SoloScriptSage/xNAV650-Ouster-Adapter-Enclosure/xnav650.kicad_sch

## KiCad design xnav650.kicad_sch (2025-11-14)

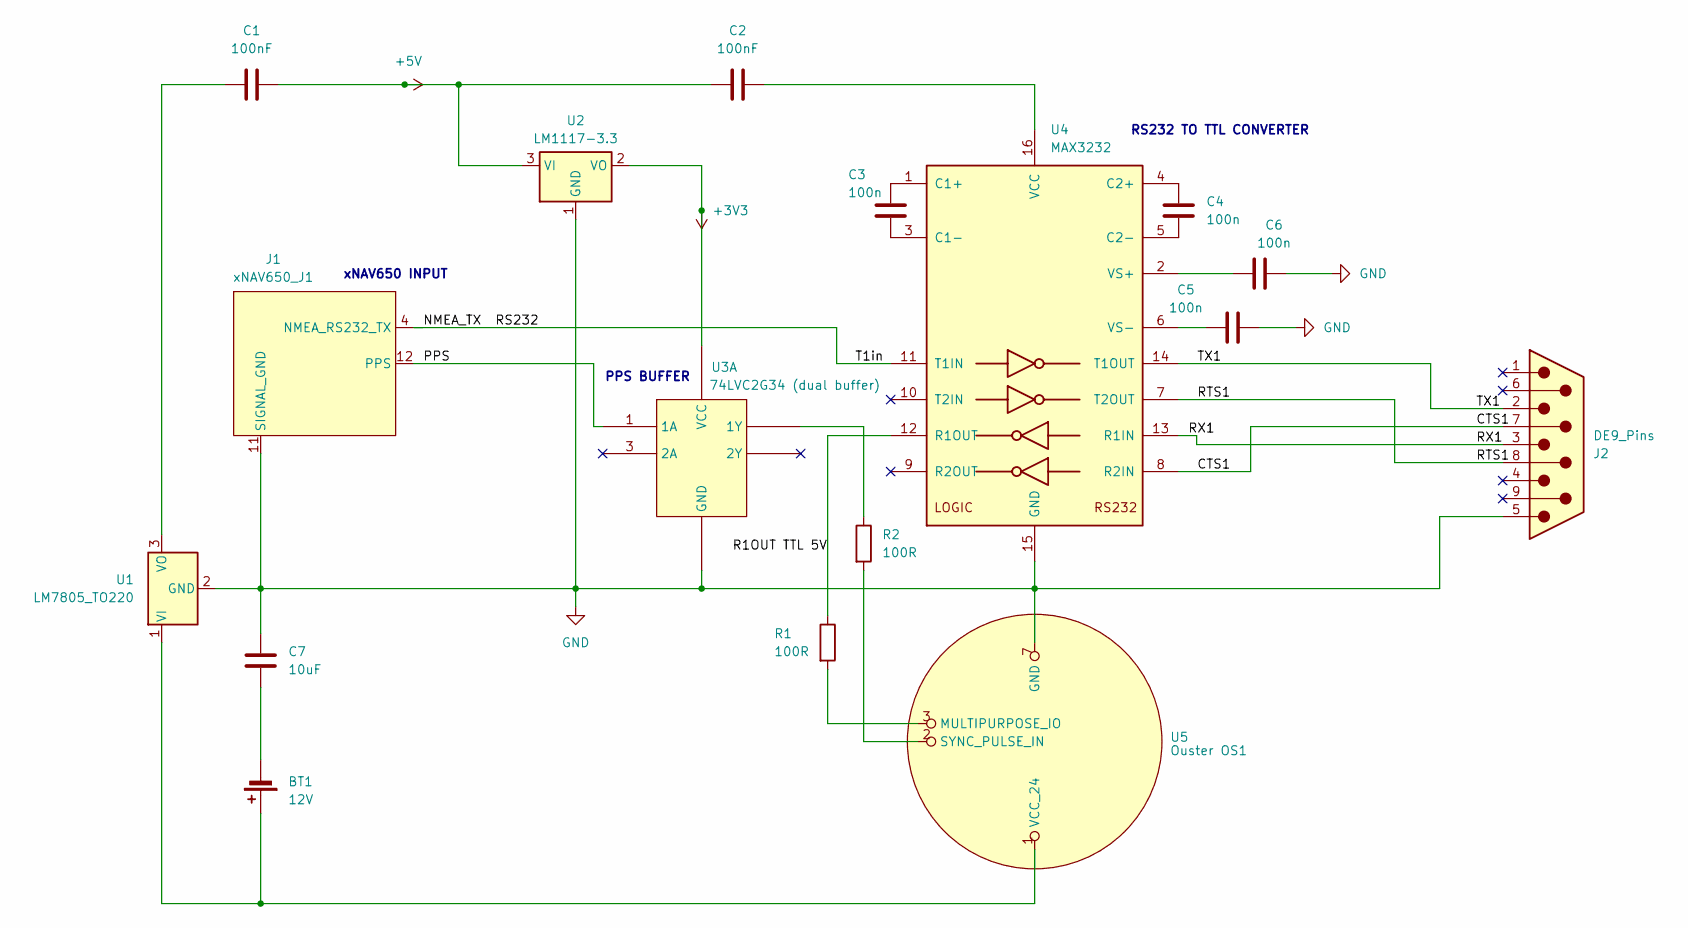
[picture p2: schematic xnav650.kicad_sch]

Parts:
BT1: 12V
C1, C2: 100nF
C3, C4, C5, C6: 100n
C7: 10uF
J1: xNAV650_J1; Micro-D-15
J2: DE9_Pins
R1, R2: 100R
U1: LM7805_TO220; TO-220-3_Vertical
U2: LM1117-3.3; TO-252-3_TabPin2
U3: 74LVC2G34 (dual buffer)
U4: MAX3232
U5: Ouster OS1

Connections:
+3V3: U2.2 (VO), U3. (VCC)
+5V: C1.2, C2.1, U2.3 (VI)
CTS1: J2.7, U4.8 (R2IN)
GND: C5.2, C6.2, C7.2, J1.11 (SIGNAL_GND), J2.5, U1.2 (GND), U2.1 (GND), U3. (VCC), U4.15 (GND), U5.7 (GND)
NMEA_TX: J1.4 (NMEA_RS232_TX), U4.11 (T1IN)
unnamed: BT1.1 (+), U1.1 (VI), U5.1 (VCC_24)
unnamed: BT1.2 (-), C7.1
unnamed: C1.1, U1.3 (VO)
unnamed: C2.2, U4.16 (VCC)
unnamed: C3.1, U4.1 (C1+)
unnamed: C3.2, U4.3 (C1-)
unnamed: C4.1, U4.4 (C2+)
unnamed: C4.2, U4.5 (C2-)
unnamed: C5.1, U4.6 (VS-)
unnamed: C6.1, U4.2 (VS+)
unnamed: R1.2, U5.3 (MULTIPURPOSE_IO)
unnamed: R2.1, U3. (VCC)
unnamed: R2.2, U5.2 (SYNC_PULSE_IN)
PPS: J1.12 (PPS), U3.1 (1A)
R1OUT TTL 5V: R1.1, U4.12 (R1OUT)
RTS1: J2.8, U4.7 (T2OUT)
RX1: J2.3, U4.13 (R1IN)
TX1: J2.2, U4.14 (T1OUT)

Notes on the sheet:
RS232 TO TTL CONVERTER
xNAV650 INPUT
PPS BUFFER
